yigithansari/MIL-STD-1275D-protection-board/images/pcb-layout/bottom-layer.png

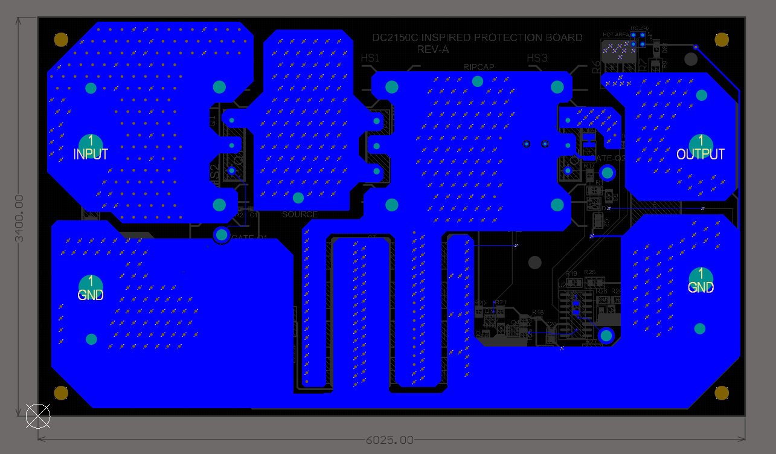
images/pcb-layout/bottom-layer.png
