yigithansari/MIL-STD-1275D-protection-board/images/pcb-layout/top-overlay.png

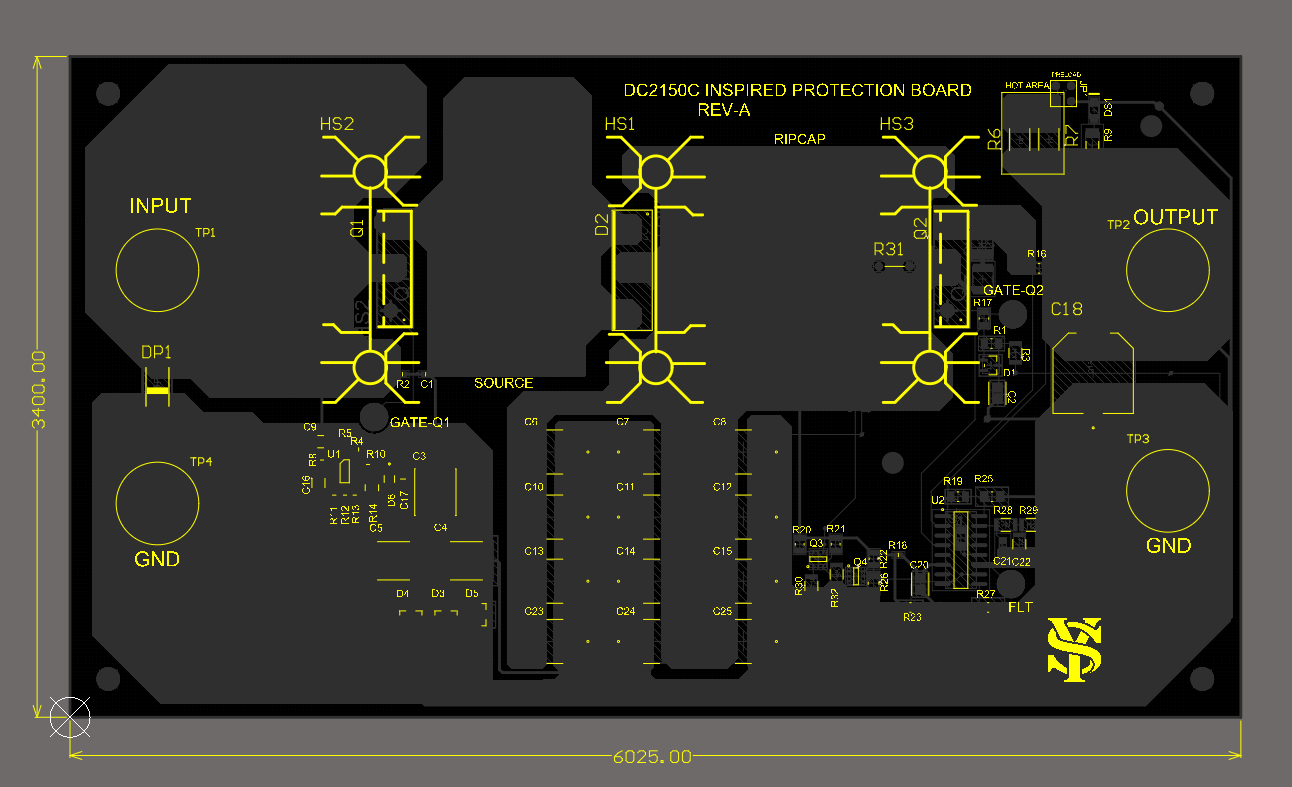
images/pcb-layout/top-overlay.png
