yigithansari/MIL-STD-1275D-protection-board/images/pcb-renders/MIL_STD_1275D-SIDE-VIEW.png

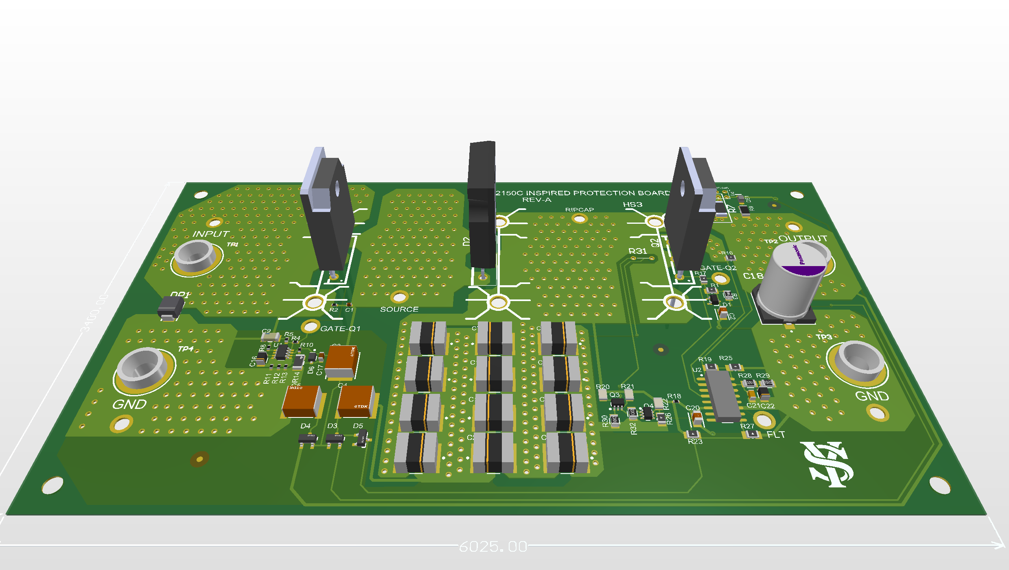
images/pcb-renders/MIL_STD_1275D-SIDE-VIEW.png
